dotrocks/esd-ip1-capacitor-design/latex/assets/3WhatsApp Image 2024-04-18 at 20.32.12.jpeg

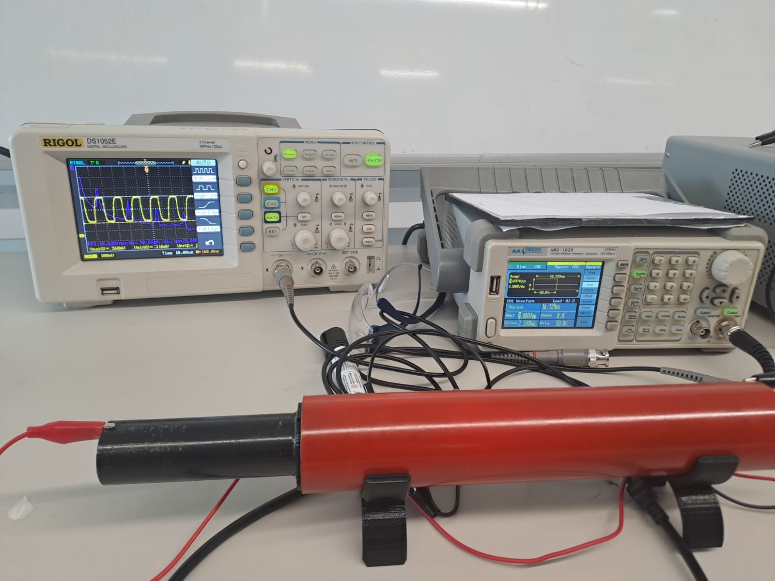
latex/assets/3WhatsApp Image 2024-04-18 at 20.32.12.jpeg
