dotrocks/esd-ip1-capacitor-design/latex/assets/20240419_120157.jpg

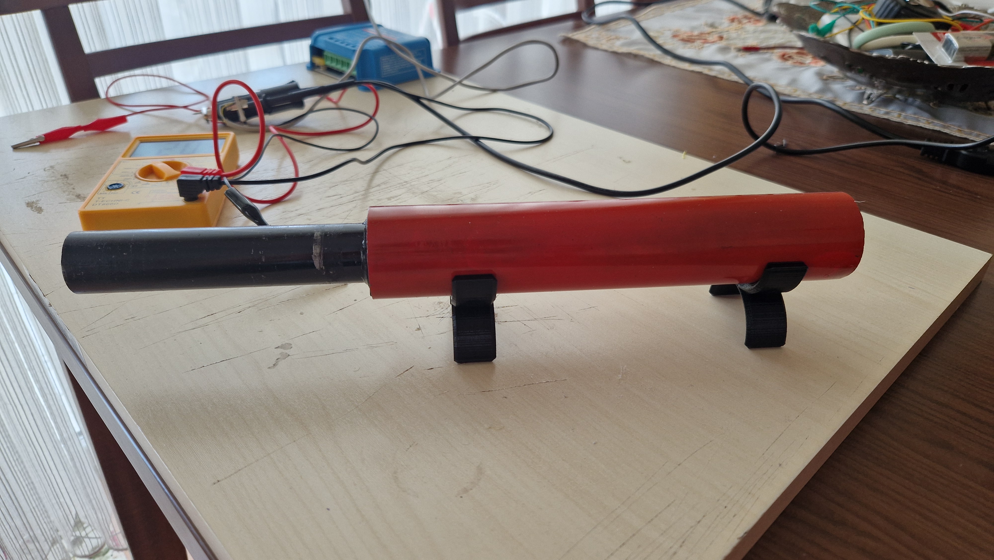
latex/assets/20240419_120157.jpg
