dotrocks/esd-ip1-capacitor-design/latex/assets/20240419_120217.jpg

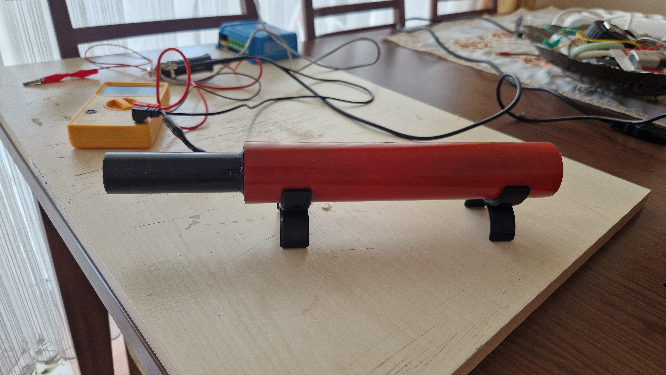
latex/assets/20240419_120217.jpg
