dotrocks/esd-ip1-capacitor-design/latex/assets/20240419_120242.jpg

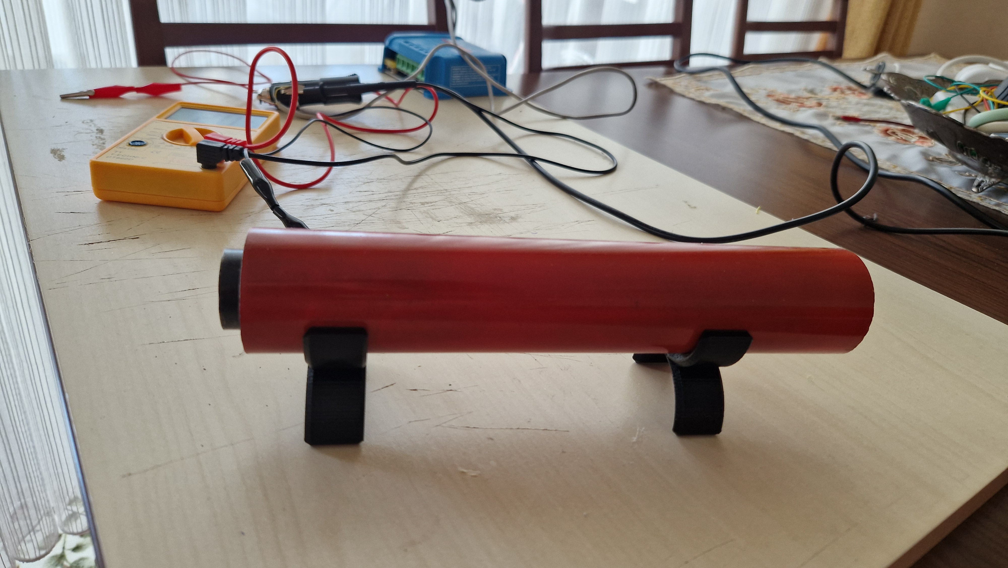
latex/assets/20240419_120242.jpg
