dotrocks/esd-ip1-capacitor-design/latex/assets/1713462629.png

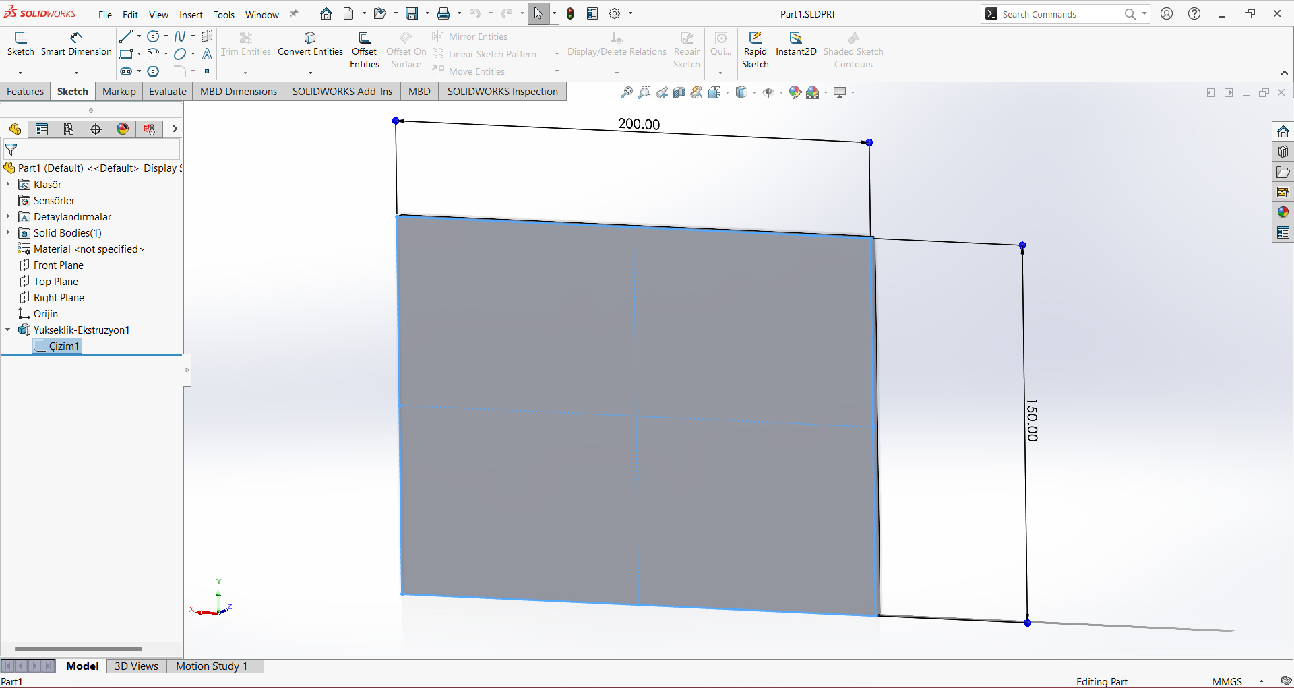
latex/assets/1713462629.png
