dotrocks/esd-ip1-capacitor-design/latex/assets/1713464718.png

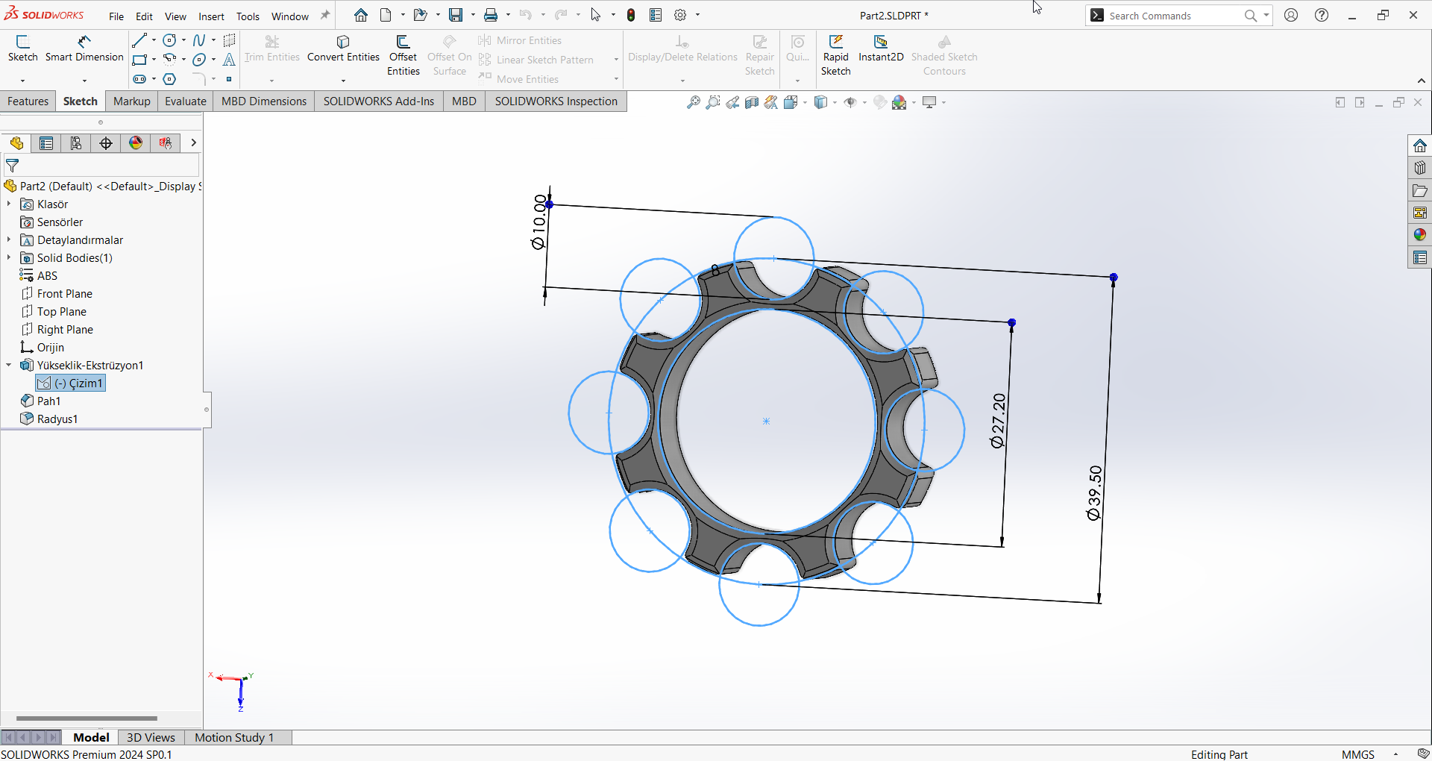
latex/assets/1713464718.png
