dotrocks/esd-ip1-capacitor-design/latex/assets/1713464755.png

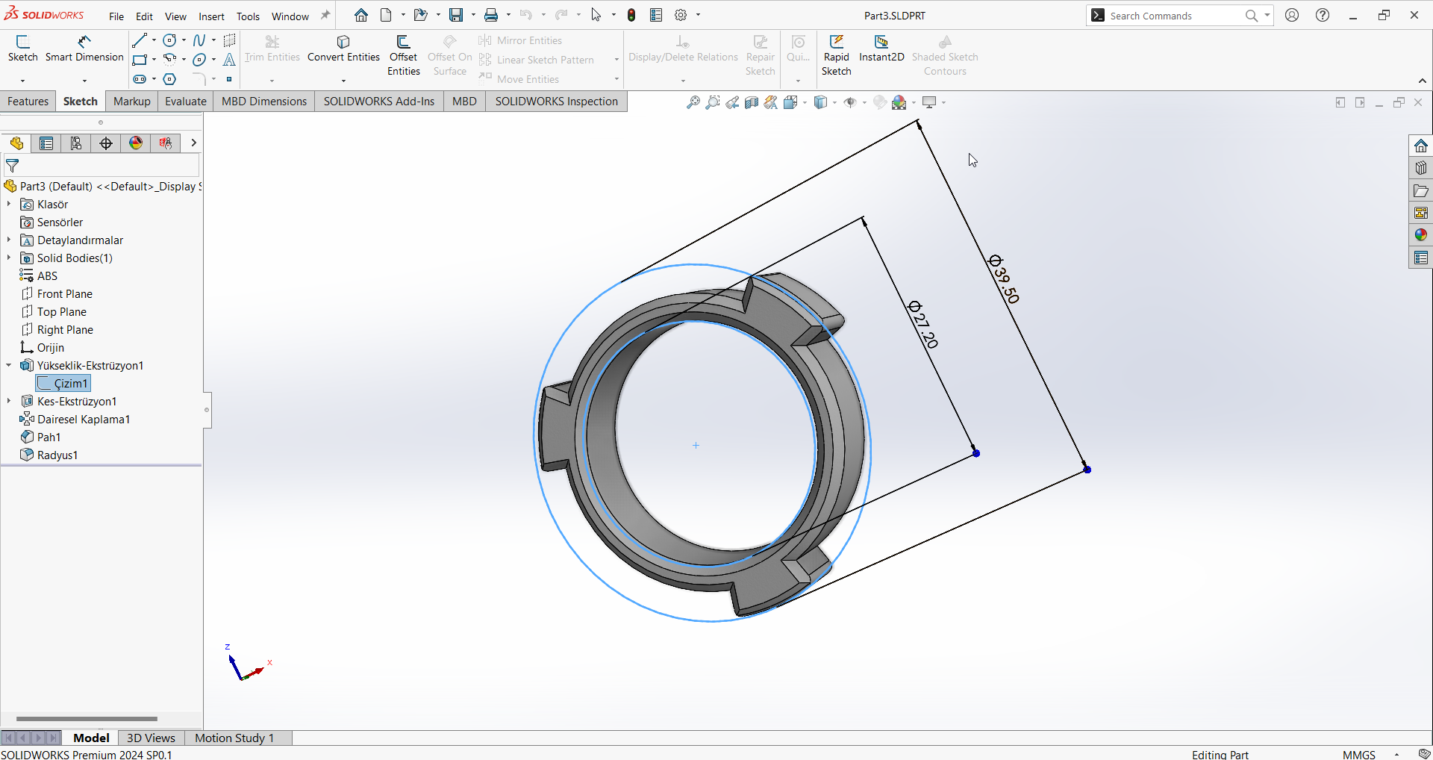
latex/assets/1713464755.png
