dotrocks/esd-ip1-capacitor-design/latex/assets/1713464809.png

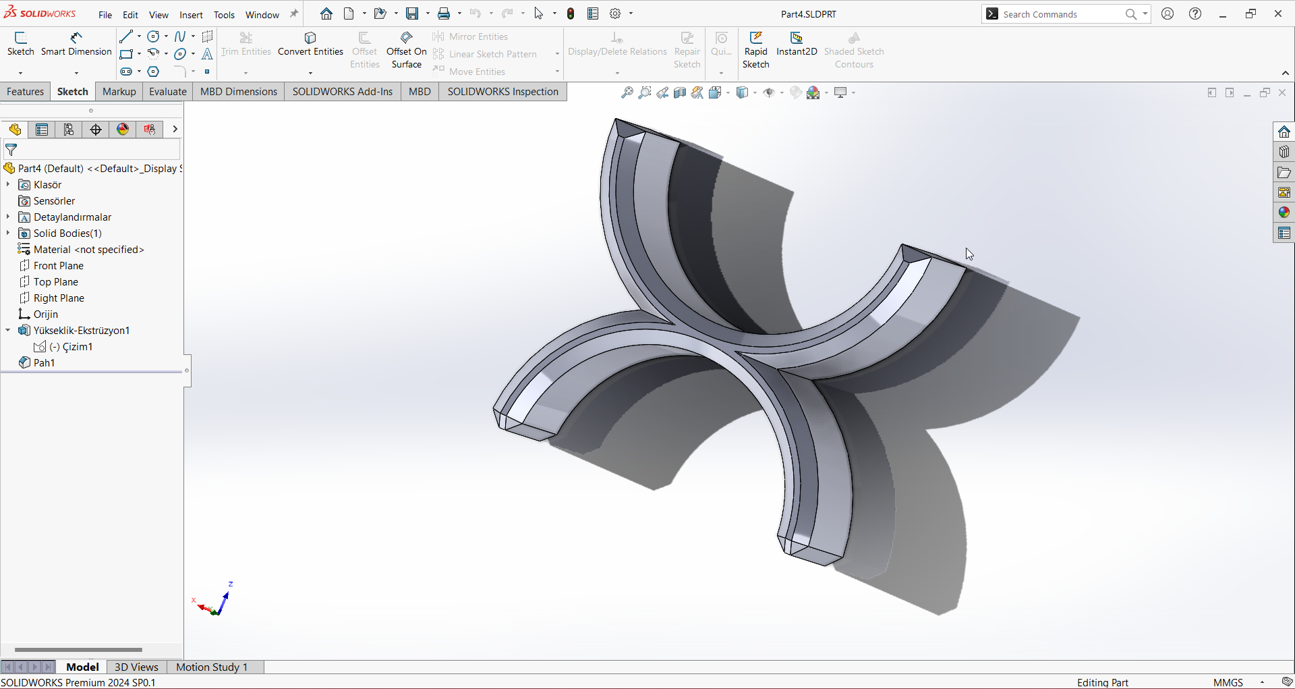
latex/assets/1713464809.png
