dotrocks/esd-ip1-capacitor-design/latex/assets/1713507546.png

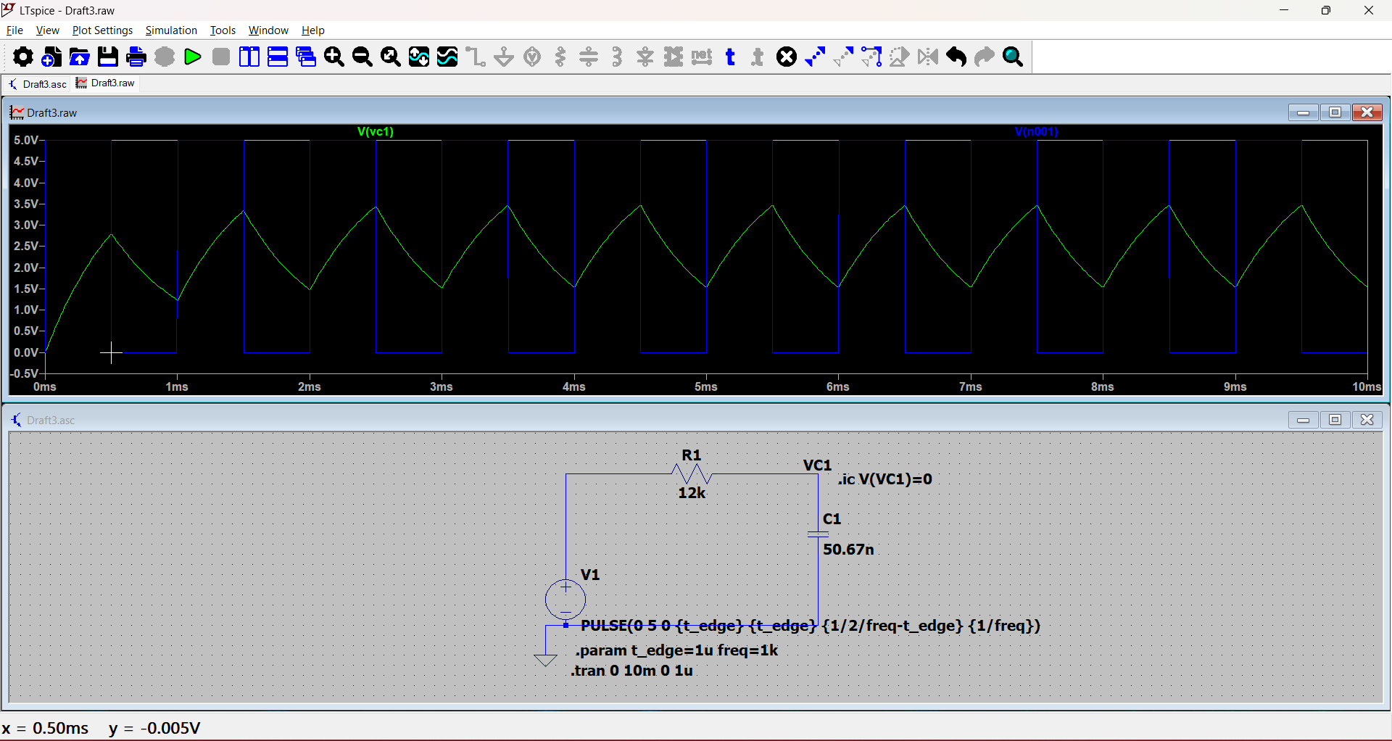
latex/assets/1713507546.png
