dotrocks/esd-ip1-capacitor-design/latex/assets/WhatsApp Image 2024-04-16 at 18.20.12 (1).jpeg

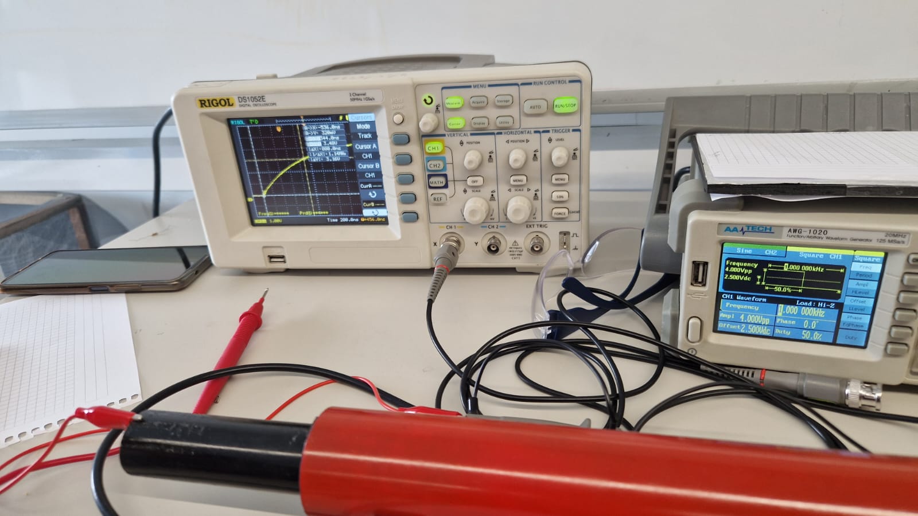
latex/assets/WhatsApp Image 2024-04-16 at 18.20.12 (1).jpeg
