dotrocks/esd-ip1-capacitor-design/latex/assets/WhatsApp Image 2024-04-18 at 20.32.11.jpeg

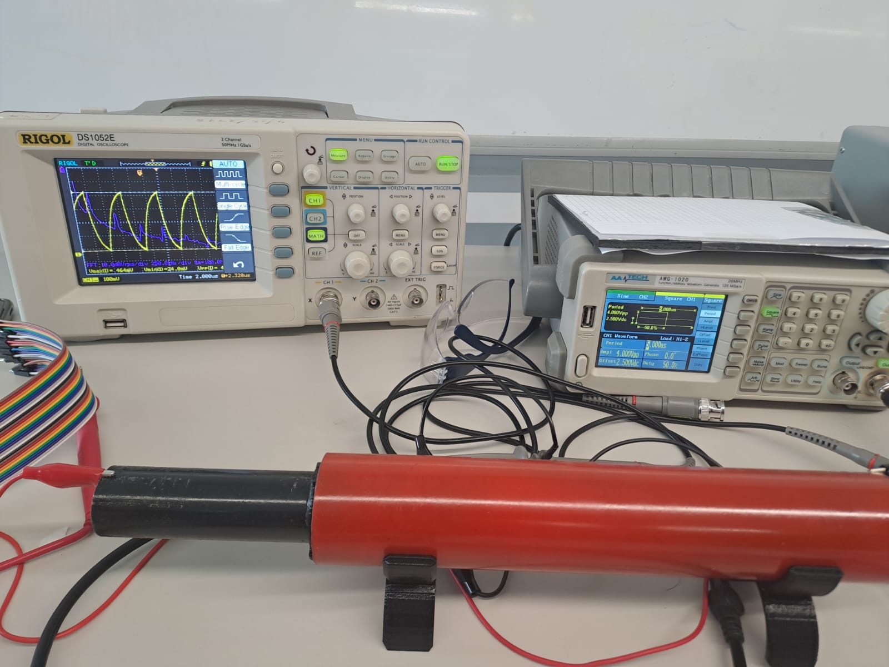
latex/assets/WhatsApp Image 2024-04-18 at 20.32.11.jpeg
